TomPotato/Rover-Embedded-Project-2024-25/Our Code/ArduinoUNO/ComponentsCode/UltrasonicSensor/UltrasonicSensor.ino

#define echoPin 11
#define trigPin 12

void setup() {
  Serial.begin (9600);
  pinMode(trigPin, OUTPUT);
  pinMode(echoPin, INPUT);
}

void loop() {
  float duration, distance;
  digitalWrite(trigPin, LOW); 
  delayMicroseconds(2);
 
  digitalWrite(trigPin, HIGH);
  delayMicroseconds(10);

  digitalWrite(trigPin, LOW);
  
  duration = pulseIn(echoPin, HIGH);
  distance = (duration / 2) * 0.0343148;
  
  if (distance >= 400){
    Serial.print("Obstacle Too Far");
    delay(20);
  }
  else if(distance <= 30){
    Serial.print("Obstacle Too Near");
    delay(20);
  }
  else {
    Serial.print("Distance = ");
    Serial.print(distance);
    Serial.println(" cm");
    delay(20);
  }
}
